gfschwengle/wmc_sensor_proto/docs/capSensor2.png

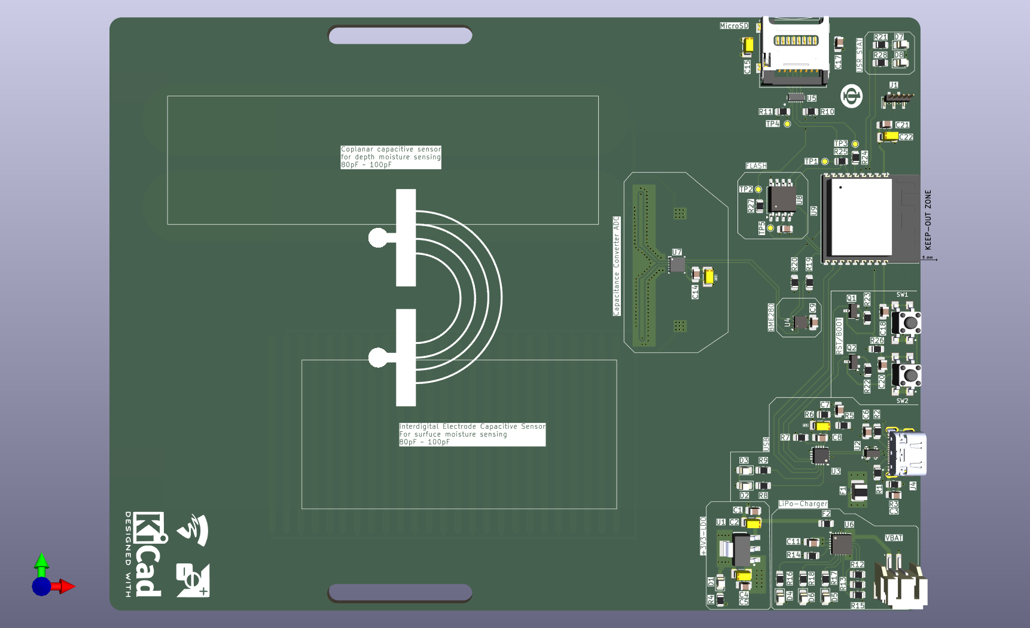
docs/capSensor2.png
