gfschwengle/wmc_sensor_proto/docs/capSensor4.png

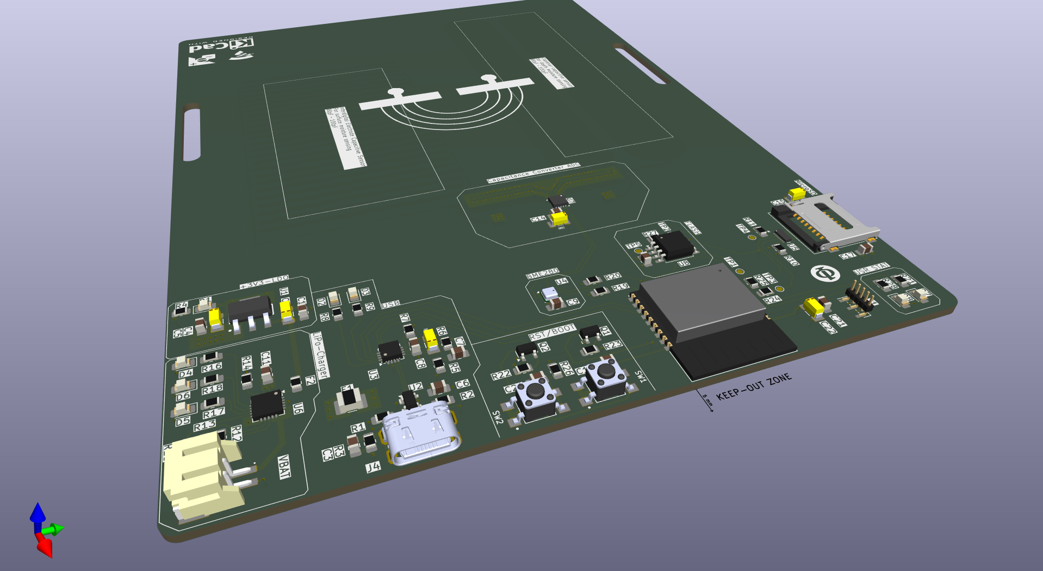
docs/capSensor4.png
