gfschwengle/wmc_sensor_proto/docs/capSensor7.png

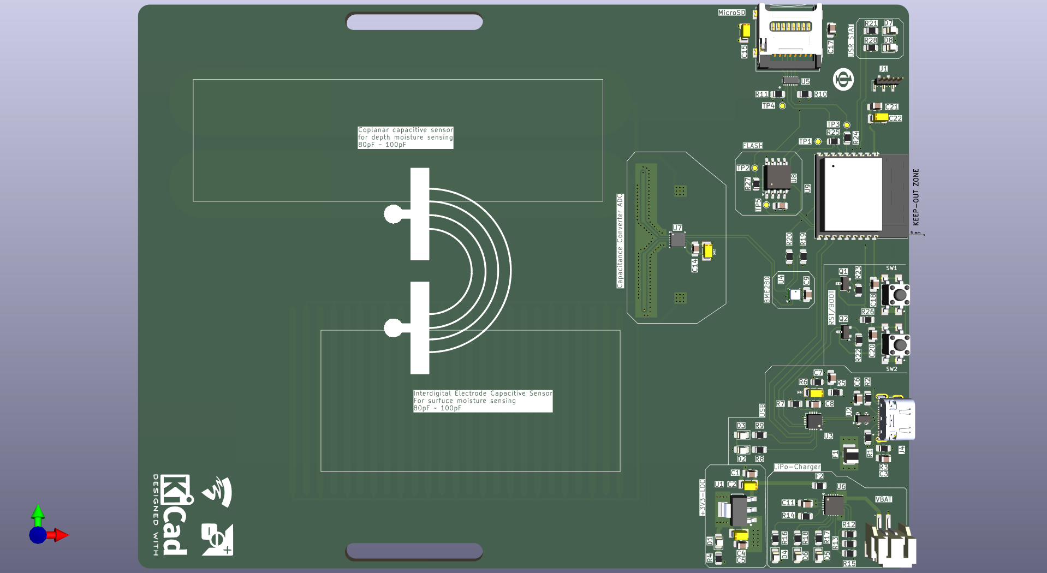
docs/capSensor7.png
