gfschwengle/wmc_sensor_proto/docs/capSensor8.png

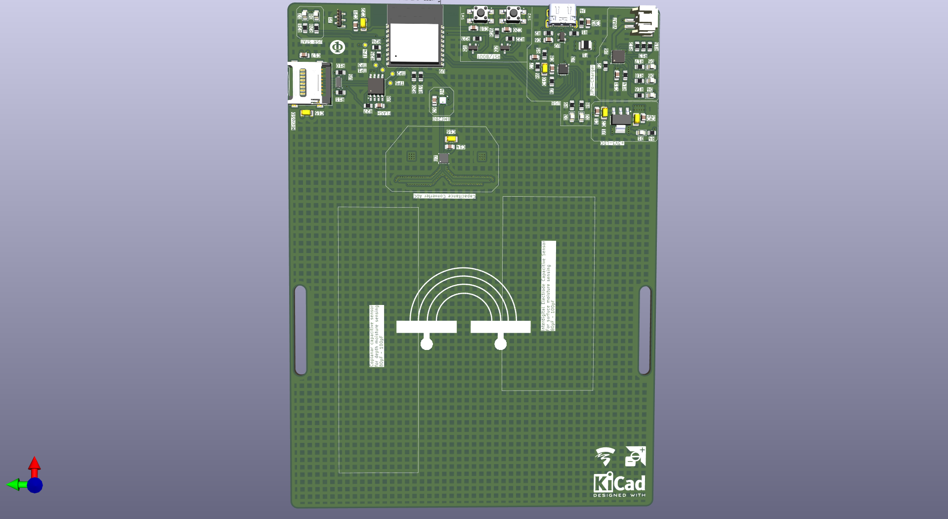
docs/capSensor8.png
