gfschwengle/wmc_sensor_proto/docs/capSensor9.png

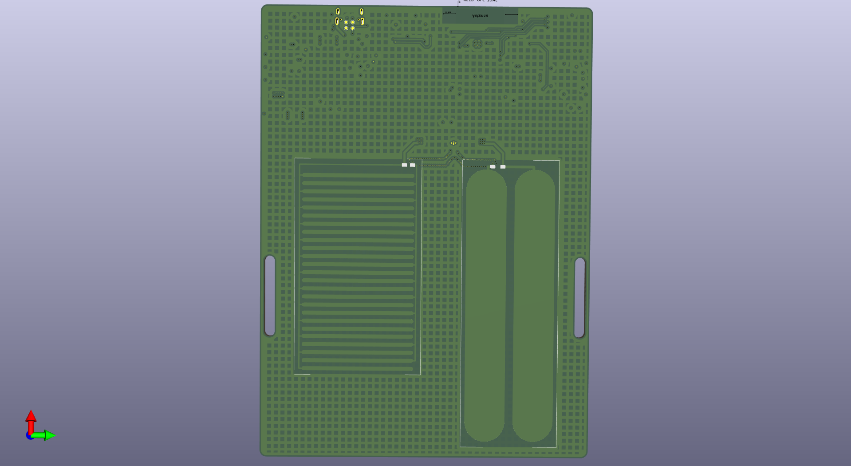
docs/capSensor9.png
