gfschwengle/wmc_sensor_proto/docs/ScyPy_Images/cap_sensor_sim.png

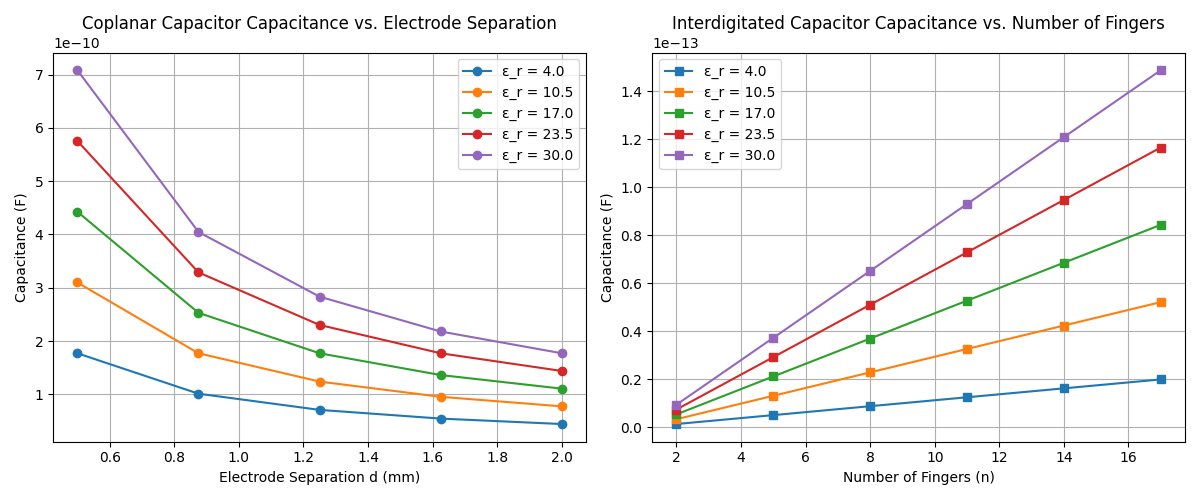
docs/ScyPy_Images/cap_sensor_sim.png
