gfschwengle/wmc_sensor_proto/docs/ScyPy_Images/CapacitiveSensorResponse_wmc.png

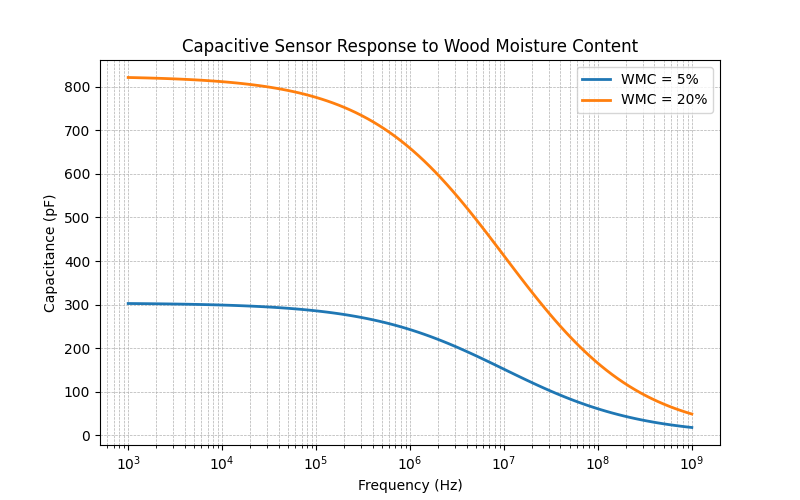
docs/ScyPy_Images/CapacitiveSensorResponse_wmc.png
